loutlot/Loutrack2/docs/README.md

# loutrack2 ドキュメント

ドキュメントを「実装前 / 実行中 / 完了 / 運用手順」に分けて管理します。
要件の起点は `context/request.md` です。

## フォルダ構成

- `docs/00_pre_implementation/`
  - 実装前の要件・理論・初期計画
  - `pre_doc/` は背景メモ・検討履歴
- `docs/10_in_progress/`
  - 現在進行中の実装手順・計画
- `docs/20_completed/`
  - 完了済み検討・実装の成果資料
- `docs/30_procedure/`
  - Pi / GUI の起動、確認、停止などの日常運用手順

## 現在の主要ドキュメント

1. `docs/00_pre_implementation/requirements_def.md`
2. `docs/00_pre_implementation/implementation_plan.md`
3. `docs/10_in_progress/gui_runbook.md`
4. `docs/20_completed/tracking_gui_plan.md`
5. `docs/20_completed/24_next_steps_wand_runbook.md`
6. `docs/30_procedure/pi_gui_start_stop.md`

## context ディレクトリの扱い

- `context/request.md`: 元要求（一次ソース）
- `context/archive/`: 過去メモ（通常は直接編集しない）
