loutlot/Loutrack2/logs/sim/passive_stabilization_v2/body_mount_mesh_lite_v1_motion.gif

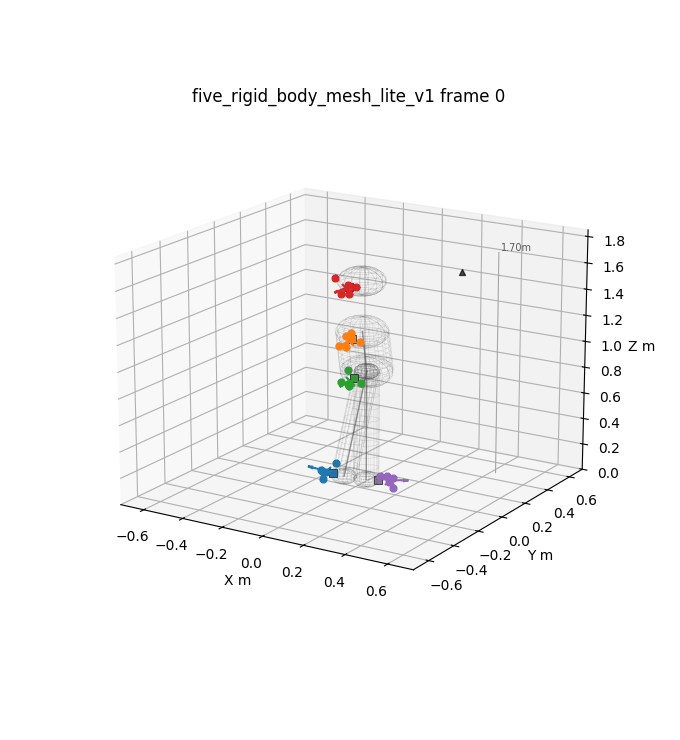
logs/sim/passive_stabilization_v2/body_mount_mesh_lite_v1_motion.gif
