loutlot/Loutrack2/logs/sim/passive_stabilization_v2/mesh_lite_1_7m_reference_preview.png

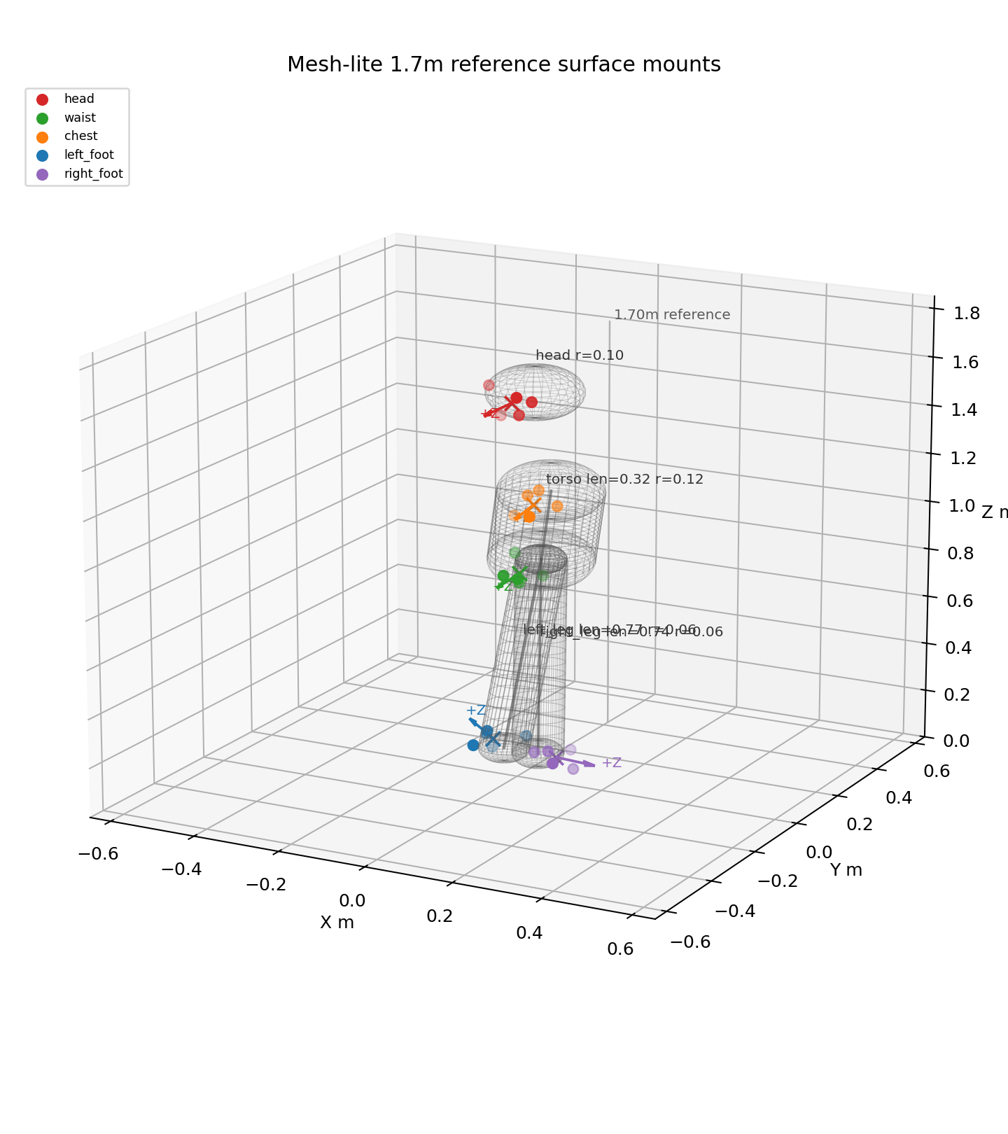
logs/sim/passive_stabilization_v2/mesh_lite_1_7m_reference_preview.png
