loutlot/Loutrack2/logs/sim/passive_stabilization_v2/mesh_lite_capsule_preview.png

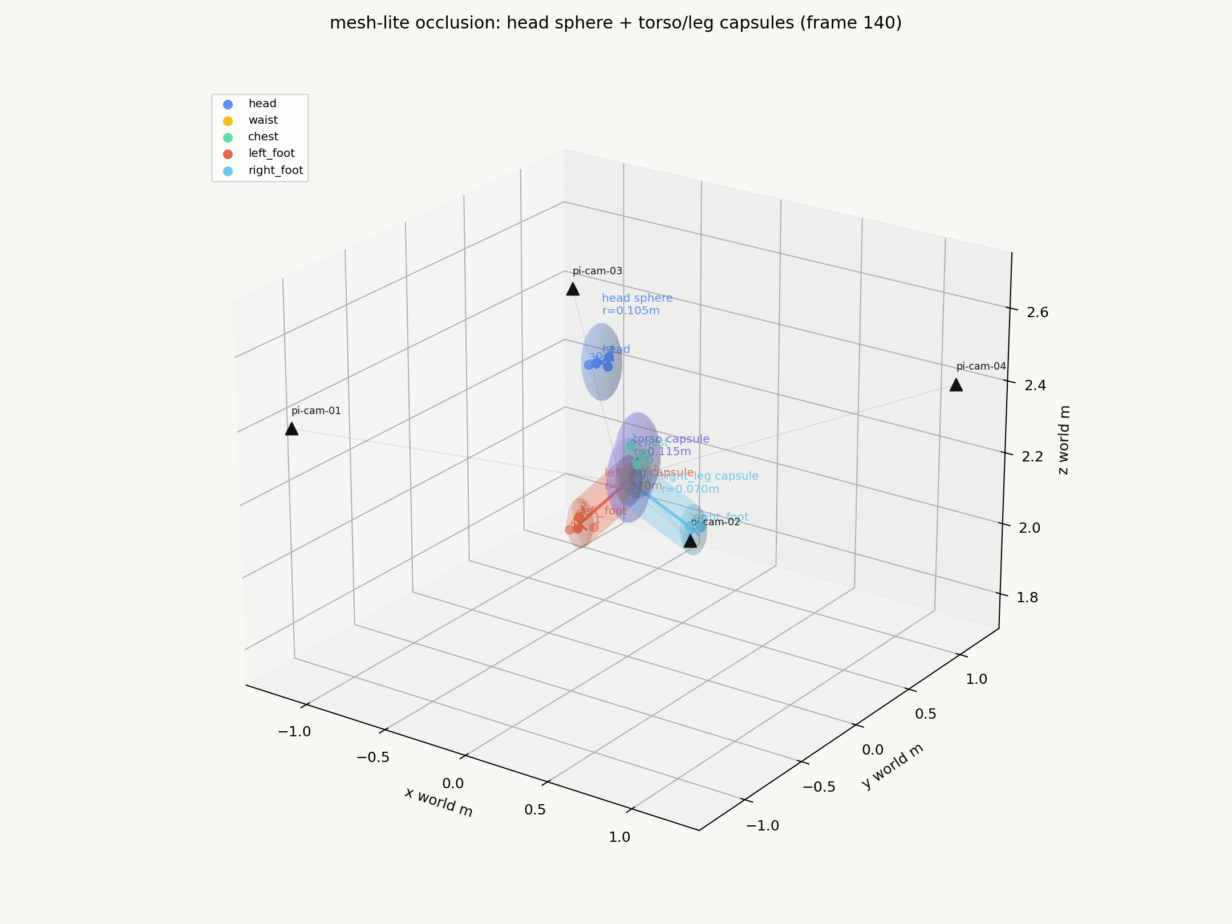
logs/sim/passive_stabilization_v2/mesh_lite_capsule_preview.png
